IanFeldman/ssd/nor-prototype-2/firmware/main.c

#include "flash.h"
#include "uart.h"

#define PROMPT "> "

void parse_input(char *input)
{
    char value;
    address_t addr;

    uart_print_esc(NEW_LINE);
    switch (input[0])
    {
        case 'r':
            uart_hex_to_addr(input + 1, &addr);
            value = flash_read(&addr);
            uart_print("Read byte 0x");
            uart_print_hex(value);
            uart_print(" from address 0x");
            uart_print_addr(&addr);
            break;
        case 'p':
            uart_hex_to_addr(input + 1, &addr);
            value = uart_hex_to_char(input + 7);
            flash_program(value, &addr);
            uart_print("Wrote byte 0x");
            uart_print_hex(value);
            uart_print(" to address 0x");
            uart_print_addr(&addr);
            break;
        case 'e':
            uart_hex_to_addr(input + 1, &addr);
            flash_erase(&addr);
            uart_print("Erased 4k sector starting at address 0x");
            uart_print_addr(&addr);
            break;
        default:
            uart_print("?");
    }
    uart_print_esc(NEW_LINE);
    uart_print(PROMPT);
    uart_reset_input_ready();
}


void main()
{
    /* initialize peripherals */
    uart_init();
    flash_init();

    /* reset screen */
    uart_print_esc(CLEAR_SCREEN);
    uart_print_esc(HOME_CURSOR);
    uart_print(PROMPT);

    while(1)
    {
        /* check if input is ready */
        if (uart_get_input_ready())
        {
            parse_input(uart_get_input());
        }
    }
}
